Solartraveler/solarclock/minimatrix/software/matrix-advancedclock/menudata-progmem.c

/*You may need to add #include <avr/pgmspace.h> where you included this file */
const unsigned char menudata[] PROGMEM = {
4, 10, 101, 0, 0, 245, 11, 9, 0, 0, 0, 2, 0, 0, 8, 0, 
0, 14, 10, 1, 1, 0, 130, 6, 10, 2, 2, 0, 0, 0, 10, 3, 
3, 0, 0, 0, 10, 100, 4, 0, 47, 1, 9, 0, 0, 0, 2, 0, 
0, 0, 70, 13, 14, 10, 2, 0, 0, 71, 0, 10, 3, 0, 0, 18, 
1, 10, 4, 4, 0, 47, 1, 9, 0, 0, 0, 2, 0, 0, 0, 76, 
13, 14, 10, 2, 0, 0, 100, 0, 10, 3, 0, 0, 42, 0, 10, 4, 
5, 0, 117, 1, 9, 0, 0, 0, 2, 0, 0, 0, 83, 13, 14, 10, 
2, 0, 0, 129, 0, 10, 3, 0, 0, 71, 0, 10, 4, 6, 0, 152, 
1, 9, 0, 0, 0, 2, 0, 0, 0, 90, 13, 14, 10, 2, 0, 0, 
158, 0, 10, 3, 0, 0, 100, 0, 10, 4, 7, 0, 187, 1, 9, 0, 
0, 0, 2, 0, 0, 0, 96, 13, 14, 10, 2, 0, 0, 187, 0, 10, 
3, 0, 0, 129, 0, 10, 4, 8, 0, 222, 1, 9, 0, 0, 0, 2, 
0, 0, 0, 101, 13, 14, 10, 2, 0, 0, 216, 0, 10, 3, 0, 0, 
158, 0, 10, 4, 0, 0, 239, 1, 9, 0, 0, 0, 2, 0, 0, 0, 
108, 13, 14, 10, 2, 0, 0, 245, 0, 10, 3, 0, 0, 187, 0, 10, 
4, 0, 0, 211, 5, 9, 0, 0, 0, 2, 0, 0, 0, 114, 13, 14, 
10, 2, 0, 0, 18, 1, 10, 3, 0, 0, 216, 0, 10, 4, 4, 0, 
34, 12, 9, 0, 0, 0, 2, 0, 0, 0, 122, 13, 15, 10, 2, 0, 
0, 42, 0, 10, 3, 0, 0, 245, 0, 10, 4, 9, 0, 34, 12, 9, 
0, 0, 0, 2, 0, 0, 8, 1, 0, 14, 10, 1, 1, 0, 42, 0, 
10, 2, 10, 0, 82, 1, 10, 3, 5, 0, 117, 1, 10, 4, 7, 0, 
187, 1, 9, 0, 0, 0, 2, 0, 0, 8, 2, 0, 14, 10, 1, 1, 
0, 42, 0, 10, 2, 4, 0, 47, 1, 10, 3, 5, 0, 117, 1, 10, 
4, 7, 0, 187, 1, 9, 0, 0, 0, 2, 0, 0, 8, 3, 0, 14, 
10, 1, 1, 0, 71, 0, 10, 2, 11, 0, 0, 0, 10, 3, 12, 0, 
0, 0, 10, 4, 13, 0, 0, 0, 9, 0, 0, 0, 2, 0, 0, 8, 
4, 0, 14, 10, 1, 1, 0, 100, 0, 10, 2, 14, 0, 0, 0, 10, 
3, 15, 0, 0, 0, 10, 4, 16, 0, 0, 0, 9, 0, 0, 0, 2, 
0, 0, 8, 5, 0, 14, 10, 1, 1, 0, 129, 0, 10, 2, 17, 0, 
0, 0, 10, 3, 18, 0, 0, 0, 10, 4, 19, 0, 0, 0, 9, 0, 
0, 0, 2, 0, 0, 8, 6, 0, 14, 10, 1, 1, 0, 158, 0, 9, 
0, 0, 0, 2, 0, 0, 0, 129, 13, 14, 10, 1, 0, 0, 187, 0, 
10, 2, 0, 0, 18, 2, 10, 3, 0, 0, 217, 3, 10, 4, 20, 0, 
252, 3, 9, 0, 0, 0, 2, 0, 0, 0, 137, 13, 14, 10, 1, 0, 
0, 187, 0, 10, 2, 0, 0, 53, 2, 10, 3, 0, 0, 239, 1, 10, 
4, 0, 0, 31, 4, 9, 0, 0, 0, 2, 0, 0, 0, 144, 13, 14, 
10, 1, 0, 0, 187, 0, 10, 2, 0, 0, 88, 2, 10, 3, 0, 0, 
18, 2, 10, 4, 0, 0, 60, 4, 9, 0, 0, 0, 2, 0, 0, 0, 
151, 13, 14, 10, 1, 0, 0, 187, 0, 10, 2, 0, 0, 123, 2, 10, 
3, 0, 0, 53, 2, 10, 4, 0, 0, 89, 4, 9, 0, 0, 0, 2, 
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
