Solartraveler/solarclock/minimatrix/software/matrix-advancedclock/rc5decoder.h

/************************************************************************/
/*                                                                      */
/*                      RC5 Remote Receiver                             */
/*                                                                      */
/*              Author: Peter Dannegger                                 */
/*                      danni@specs.de                                  */
/*                                                                      */
/************************************************************************/

//connected to PC2
//on of switch on PC1

void rc5Init(void);
void rc5Stop(void);

uint16_t rc5getdata(void);
