Solartraveler/solarclock/minimatrix/software/matrix-advancedclock/gui.c

/* Matrix-Advancedclock
  (c) 2014-2018 by Malte Marwedel
  www.marwedels.de/malte

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
    You should have received a copy of the GNU General Public License
    along with this program; if not, write to the Free Software
    Foundation, Inc., 59 Temple Place, Suite 330, Boston, MA  02111-1307  USA
*/

/* The GUI logic. No AVR specific functions (except loading from flash)
within this file, allows compiling and testing the whole GUI on a PC.
*/

#include <string.h>
#include <stdio.h>
#include <stdint.h>
#include <ctype.h>

#include "config.h"
#include "timeconvert.h"

/*Enable for debug builds.
  Can result in crashes or dark display with no way to get back without
  clearing the EEPRom with a programmer
*/
//#define UNSAFE_OPS

#ifndef PC_BUILD
//AVR only
#include <avr/pgmspace.h>
#include "main.h"
#include "dcf77.h"
#include "displayRtc.h"
#include "rs232.h"
#include "pintest.h"
#include "sound.h"

#else
//PC compatibility layer
#define PROGMEM
#define PSTR(X) X
#define sprintf_P sprintf
#define reboot() printf("reboot()\r\n")
#define dcf77_disable() printf("DCF77 disabled\r\n")
#define dcf77_enable(X) printf("DCF77 enabled\r\n")
#define disp_configure_set(X, Y) printf("disp_configure_set(%i, %i);\r\n", X, Y)
#define rs232_rx_disable() printf("rs232_rx_disable()\r\n")
#define rs232_rx_init() printf("rs232_rx_init()\r\n")
#define pintest_runtest() 0
#define sound_beep(X, Y, Z)

void dcf77_getstatus(char* text);
unsigned char pgm_read_byte(const unsigned char * addr) {
	return *addr;
}

#endif

#include "gui.h"
#include "config.h"

#include "menu-interpreter.h"
#include "menudata-progmem.c"

#define CHARS_PER_MENU_TEXT 14

unsigned char g_StringMenus[MENU_TEXT_MAX*CHARS_PER_MENU_TEXT];

dispUpdateFunc * g_dispUpdate; //NULL is a legitimate value



unsigned char menu_byte_get(MENUADDR addr) {
	if (addr >= MENU_DATASIZE) {
		return 0;
	}
	return pgm_read_byte(menudata+addr);
}

uint8_t updateVoltageText(void) {
	sprintf_P((char*)menu_strings[MENU_TEXT_InputVoltage], PSTR("%umV"), g_state.batVoltage);
	return 1;
}

uint8_t updateCurrentText(void) {
	sprintf_P((char*)menu_strings[MENU_TEXT_ChargerCurrent], PSTR("%imA"), g_state.chargerCurrent);
	return 1;
}

uint8_t updateDcf77Text(void) {
	dcf77_getstatus((char*)menu_strings[MENU_TEXT_DcfValue]);
	return 1;
}

/*
The static variable helps caching the text printing and avoiding calls to
menu_update if nothing changed
*/
uint8_t updateClockTextGeneric(uint8_t clockShowSeconds) {
	static uint8_t slast = 255;
	static uint8_t mlast = 255;
	static uint8_t hlast = 255;
	static uint8_t clockShowSecondslast = 255;
	uint8_t s = g_state.timescache;
	uint8_t m = g_state.timemcache;
	uint8_t h = g_state.timehcache;
	if ((clockShowSeconds != clockShowSecondslast) || (mlast != m) ||
	    (hlast != h) || ((slast != s) && (clockShowSeconds))) {
		clockShowSecondslast = clockShowSeconds;
		slast = s;
		mlast = m;
		hlast = h;
		if (clockShowSeconds) {
			sprintf_P((char*)menu_strings[MENU_TEXT_Clock], PSTR("%2i:%02i:%02i"), h, m, s);
			if (h < 10) {
				menu_strings[MENU_TEXT_Clock][0] = '\t';
			}
		} else {
			sprintf_P((char*)menu_strings[MENU_TEXT_Clock], PSTR("     %2i:%02i"), h, m);
			if (h < 10) {
				menu_strings[MENU_TEXT_Clock][5] = '\t';
			}
		}
		return 1;
	}
	return 0;
}

uint8_t updateClockText(void) {
	return updateClockTextGeneric(g_settings.clockShowSeconds);
}

uint8_t updateClockSetText(void) {
	return updateClockTextGeneric(1);
}

uint8_t updateDateText(void) {
	static uint32_t timelast = 0;
	uint32_t temp = g_state.time;
	if (temp != timelast) {
		timelast = temp;
		uint8_t y;
		uint8_t month;
		uint8_t d;
		dateFromTimestamp(temp, &d, &month, &y, NULL);
		month++; //starts with 0
		d++; //starts with 0
		sprintf_P((char*)menu_strings[MENU_TEXT_Date], PSTR("%02i.%02i.%2i"), (uint16_t)d, (uint16_t)month, (uint16_t)y);
		return 1;
	}
	return 0;
}

uint8_t updateTemperatureText(void) {
	static uint16_t gradcelsiuslast = 0xFFFF;
	if (g_state.gradcelsius10 != gradcelsiuslast) {
		gradcelsiuslast = g_state.gradcelsius10;
		uint16_t gradcelsius10th = g_state.gradcelsius10 % 10;
		uint8_t gradcelsius = g_state.gradcelsius10 / 10;
		sprintf_P((char*)menu_strings[MENU_TEXT_Temperature], PSTR( "%i.%u°C"), gradcelsius, gradcelsius10th);
		return 1;
	}
	return 0;
}

uint8_t updateKeysText(void) {
	sprintf_P((char*)menu_strings[MENU_TEXT_KeyAdValue], PSTR("B:%i"), g_state.keyDebugAd);
	return 1;
}

uint8_t updateConsumptionText(void) {
	uint32_t mah = (g_state.consumption/((uint64_t)60*(uint64_t)60*(uint64_t)1000));
	sprintf_P((char*)menu_strings[MENU_TEXT_ConsumptionTotal], PSTR("%lumAh"), (unsigned long)mah);
	return 1;
}

uint8_t updateAlarmText(void) {
	sprintf_P((char*)menu_strings[MENU_TEXT_Alarm], PSTR("%2i:%02i %s"), g_settings.alarmHour[0], g_settings.alarmMinute[0], g_settings.alarmEnabled[0] ? "On": "--");
	if (g_settings.alarmHour[0] < 10) {
		menu_strings[MENU_TEXT_Alarm][0] = '\t';
	}
	if ((g_state.subsecond & 0x6) == 0) {
		if (g_state.alarmEnterState == 0) {
			menu_strings[MENU_TEXT_Alarm][0] = '\t';
			menu_strings[MENU_TEXT_Alarm][1] = '\t';
		} else if (g_state.alarmEnterState == 1) {
			menu_strings[MENU_TEXT_Alarm][3] = '\t';
			menu_strings[MENU_TEXT_Alarm][4] = '\t';
		} else {
			menu_strings[MENU_TEXT_Alarm][6] = '\t';
			menu_strings[MENU_TEXT_Alarm][7] = '\t';
		}
	}
	return 1;
}

uint8_t updateAlarmadvancedText(void) {
	if (g_state.alarmEnterState <= 2) {
		sprintf_P((char*)menu_strings[MENU_TEXT_Alarmadvanced], PSTR("%2i:%02i %s"), g_settings.alarmHour[1], g_settings.alarmMinute[1], g_settings.alarmEnabled[1] ? "On": "--");
		if (g_settings.alarmHour[1] < 10) {
			menu_strings[MENU_TEXT_Alarmadvanced][0] = '\t';
		}
		if ((g_state.subsecond & 0x6) == 0) {
			if (g_state.alarmEnterState == 0) {
				menu_strings[MENU_TEXT_Alarmadvanced][0] = '\t';
				menu_strings[MENU_TEXT_Alarmadvanced][1] = '\t';
			} else if (g_state.alarmEnterState == 1) {
				menu_strings[MENU_TEXT_Alarmadvanced][3] = '\t';
				menu_strings[MENU_TEXT_Alarmadvanced][4] = '\t';
			} else {
				menu_strings[MENU_TEXT_Alarmadvanced][6] = '\t';
				menu_strings[MENU_TEXT_Alarmadvanced][7] = '\t';
			}
		}
	} else {
		//print enabled weekdays
		uint8_t i;
		uint8_t bitmask = g_settings.alarmWeekdays[1];
		for (i = 0; i < 7; i++) {
			if ((i == g_state.alarmEnterState - 3) && ((g_state.subsecond & 0x6) == 0)) {
				//the value currently edited
				menu_strings[MENU_TEXT_Alarmadvanced][i] = '_';
			} else {
				if (bitmask & 1) {
					menu_strings[MENU_TEXT_Alarmadvanced][i] = '1'+i; //enabled weekday
				} else {
					menu_strings[MENU_TEXT_Alarmadvanced][i] = '-'; //not enabled
				}
			}
			bitmask >>= 1;
		}
	}
	return 1;
}

uint8_t updatePowersavestartText(void) {
	sprintf_P((char*)menu_strings[MENU_TEXT_Powersavestart], PSTR("%2i:%02i"), g_settings.powersaveHourStart, g_settings.powersaveMinuteStart);
	if (g_settings.powersaveHourStart < 10) {
		menu_strings[MENU_TEXT_Powersavestart][0] = '\t';
	}
	if ((g_state.subsecond & 0x6) == 0) {
		if (g_state.powersaveenterstate == 0) {
			menu_strings[MENU_TEXT_Powersavestart][0] = '\t';
			menu_strings[MENU_TEXT_Powersavestart][1] = '\t';
		} else {
			menu_strings[MENU_TEXT_Powersavestart][3] = '\t';
			menu_strings[MENU_TEXT_Powersavestart][4] = '\t';
		}
	}
	return 1;
}

uint8_t updatePowersavestopText(void) {
	sprintf_P((char*)menu_strings[MENU_TEXT_Powersavestop], PSTR("%2i:%02i"), g_settings.powersaveHourStop, g_settings.powersaveMinuteStop);
	if (g_settings.powersaveHourStop < 10) {
		menu_strings[MENU_TEXT_Powersavestop][0] = '\t';
	}
	if ((g_state.subsecond & 0x6) == 0) {
		if (g_state.powersaveenterstate == 0) {
			menu_strings[MENU_TEXT_Powersavestop][0] = '\t';
			menu_strings[MENU_TEXT_Powersavestop][1] = '\t';
		} else {
			menu_strings[MENU_TEXT_Powersavestop][3] = '\t';
			menu_strings[MENU_TEXT_Powersavestop][4] = '\t';
		}
	}
	return 1;
}

uint8_t updatePowersaveweekText(void) {
	uint8_t i;
	uint8_t mask = g_settings.powersaveWeekdays;
	for (i = 0; i < 7; i++) {
		if ((g_state.powersaveenterstate == i) && ((g_state.subsecond & 0x6) == 0)) {
			menu_strings[MENU_TEXT_Powersaveweekdays][i] = '_';
		} else {
			if (mask & 1) {
				menu_strings[MENU_TEXT_Powersaveweekdays][i] = '1'+i;
			} else {
				menu_strings[MENU_TEXT_Powersaveweekdays][i] = '-';
			}
		}
		mask >>= 1;
	}
	return 1;
}

uint8_t updateTimerText(void) {
	if (g_state.timerCountdownSecs) {
		uint8_t h = g_state.timerCountdownSecs / (60*60);
		uint8_t m = g_state.timerCountdownSecs / 60 % 60;
		uint8_t s = g_state.timerCountdownSecs % 60;
		if (h < 10) {
			sprintf_P((char*)menu_strings[MENU_TEXT_Timer], PSTR("   %i:%02i:%02i"), h, m, s);
		} else {
			sprintf_P((char*)menu_strings[MENU_TEXT_Timer], PSTR("%i:%02i:%02i"), h, m, s);
		}
	} else {
		sprintf_P((char*)menu_strings[MENU_TEXT_Timer], PSTR("%imin"), g_settings.timerMinutes);
	}
	return 1;
}

//direct A/D value from LDR
uint8_t updateLightText(void) {
	uint8_t workmode = g_state.ldr >> 14;
	sprintf_P((char*)menu_strings[MENU_TEXT_Light], PSTR("%i:%i"), workmode, g_state.ldr & 0x3FFF);
	return 1;
}

uint8_t updateChargedText(void) {
	uint16_t mah = 0;
	mah = g_state.batteryCharged / (60*60);
	sprintf_P((char*)menu_strings[MENU_TEXT_ChargerCharged], PSTR("%umAh"), mah);
	return 1;
}

//value for driving the display
uint8_t updateDispbrightText(void) {
	if (g_settings.brightnessAuto) {
		sprintf_P((char*)menu_strings[MENU_TEXT_Brightness], PSTR("%i<%i"), g_state.brightnessLdr, g_settings.brightness);
	} else {
		sprintf_P((char*)menu_strings[MENU_TEXT_Brightness], PSTR("%i>%i"), g_state.brightnessLdr, g_settings.brightness);
	}
	return 1;
}

uint8_t updatePerformanceText(void) {
	unsigned int rcperc = g_state.performanceRcRunning * 100 / 256;
	unsigned int cpuperc = g_state.performanceCpuRunning * 100 / 256;
	sprintf_P((char*)menu_strings[MENU_TEXT_Performance], PSTR("%u%%%u%%"), rcperc, cpuperc);
	return 1;
}

uint8_t updateElapsedtimeText(void) {
	uint32_t temp = g_settings.usageseconds;
	uint16_t days = temp / (60UL*60UL*24UL);
	sprintf_P((char*)menu_strings[MENU_TEXT_Elapsedtimemeter], PSTR("%ud"), days);
	return 1;
}

uint8_t updateRc5codeText(void) {
	sprintf_P((char*)menu_strings[MENU_TEXT_Rc5up], PSTR("U:%u"), g_settings.rc5codes[2]);
	sprintf_P((char*)menu_strings[MENU_TEXT_Rc5down], PSTR("D:%u"), g_settings.rc5codes[1]);
	sprintf_P((char*)menu_strings[MENU_TEXT_Rc5left], PSTR("L:%u"), g_settings.rc5codes[0]);
	sprintf_P((char*)menu_strings[MENU_TEXT_Rc5right], PSTR("R:%u"), g_settings.rc5codes[3]);
	return 1;
}

uint8_t updateLoggerText(void) {
	sprintf_P((char*)menu_strings[MENU_TEXT_Logger], PSTR("%ik:%u"), g_state.logger.ksize, g_state.logger.nextentry);
	return 1;
}

uint8_t updateRamText(void) {
	sprintf_P((char*)menu_strings[MENU_TEXT_FreeRam], PSTR("%iByte"), (int)(g_state.memMinStack - g_state.memMaxHeap));
	return 1;
}

/*This function updates all text, which are only changed as response to user
 input. (Not as response to A/D changes or timings*/
static void updateText(void) {
	if (g_settings.debugRs232) {
		sprintf_P((char*)menu_strings[MENU_TEXT_Rs232Debug], PSTR("Dbg On %X"), g_settings.debugRs232);
	} else {
		sprintf_P((char*)menu_strings[MENU_TEXT_Rs232Debug], PSTR("Dbg Off"));
	}
	sprintf_P((char*)menu_strings[MENU_TEXT_Refresh], PSTR("%iHz"), g_settings.displayRefresh);
	sprintf_P((char*)menu_strings[MENU_TEXT_SoundFreq], PSTR("%iHz"), g_settings.soundFrequency);
	sprintf_P((char*)menu_strings[MENU_TEXT_SoundVolume], PSTR("Vol %i"), g_settings.soundVolume);
	sprintf_P((char*)menu_strings[MENU_TEXT_SoundAutoOffTime], PSTR("%imin"), g_settings.soundAutoOffMinutes);
	sprintf_P((char*)menu_strings[MENU_TEXT_BatCap], PSTR("%imAh"), g_settings.batteryCapacity);
	sprintf_P((char*)menu_strings[MENU_TEXT_LedCurrent], PSTR("%iµA"), g_settings.consumptionLedOneMax);
	sprintf_P((char*)menu_strings[MENU_TEXT_CalibRes], PSTR("%i0mΩ"), g_settings.currentResCal);
	sprintf_P((char*)menu_strings[MENU_TEXT_Dcf77Level], PSTR("E<=%i"), g_settings.dcf77Level);
	sprintf_P((char*)menu_strings[MENU_TEXT_Rebootcounter], PSTR("%lu"), (long)g_settings.reboots);
	sprintf_P((char*)menu_strings[MENU_TEXT_Dcf77Period], PSTR("D P: %ih"), g_settings.dcf77Period);
	sprintf_P((char*)menu_strings[MENU_TEXT_LoggerPeriod], PSTR("L P: %ih"), g_settings.loggerPeriod);
	sprintf_P((char*)menu_strings[MENU_TEXT_ClockCalibrate], PSTR("%ims/d"), g_settings.timeCalib);
	sprintf_P((char*)menu_strings[MENU_TEXT_Powersavebattery], PSTR("<%u%%"), g_settings.powersaveBatteryBelow);
	if (g_settings.clockShowSeconds) {
		sprintf_P((char*)menu_strings[MENU_TEXT_ShowSecs], PSTR("Sec On"));
	} else {
		sprintf_P((char*)menu_strings[MENU_TEXT_ShowSecs], PSTR("Sec Off"));
	}
	if (g_settings.brightnessNoOff) {
		sprintf_P((char*)menu_strings[MENU_TEXT_BrigthAlways], PSTR("Min Br 1"));
	} else {
		sprintf_P((char*)menu_strings[MENU_TEXT_BrigthAlways], PSTR("Min Br 0"));
	}
	if (g_settings.chargerMode == 0) {
		sprintf_P((char*)menu_strings[MENU_TEXT_ChargerMode], PSTR("Auto"));
	} else if (g_settings.chargerMode == 1) {
		sprintf_P((char*)menu_strings[MENU_TEXT_ChargerMode], PSTR("Off"));
	} else {
		sprintf_P((char*)menu_strings[MENU_TEXT_ChargerMode], PSTR("On"));
	}
	if (g_settings.rfm12mode == 0) {
		sprintf_P((char*)menu_strings[MENU_TEXT_Rfm12enabled], PSTR("Alw off"));
	} else if (g_settings.rfm12mode == 1) {
		sprintf_P((char*)menu_strings[MENU_TEXT_Rfm12enabled], PSTR("OD 1min"));
	} else if (g_settings.rfm12mode == 2) {
		sprintf_P((char*)menu_strings[MENU_TEXT_Rfm12enabled], PSTR("OD 5min"));
	} else if (g_settings.rfm12mode == 3) {
		sprintf_P((char*)menu_strings[MENU_TEXT_Rfm12enabled], PSTR("Alw on"));
	}
	if (g_settings.rc5mode == 0) {
		sprintf_P((char*)menu_strings[MENU_TEXT_Rc5enabled], PSTR("Alw off"));
	} else if (g_settings.rc5mode == 1) {
		sprintf_P((char*)menu_strings[MENU_TEXT_Rc5enabled], PSTR("OD 1min"));
	} else if (g_settings.rc5mode == 2) {
		sprintf_P((char*)menu_strings[MENU_TEXT_Rc5enabled], PSTR("OD 5min"));
	} else if (g_settings.rc5mode == 3) {
		sprintf_P((char*)menu_strings[MENU_TEXT_Rc5enabled], PSTR("Alw on"));
	}
	if (g_state.pintesterrors) {
		sprintf_P((char*)menu_strings[MENU_TEXT_Pintest], PSTR("Fail"));
	} else {
		sprintf_P((char*)menu_strings[MENU_TEXT_Pintest], PSTR("OK"));
	}
	if (g_settings.summertimeadjust) {
		sprintf_P((char*)menu_strings[MENU_TEXT_Summertime], PSTR("Adj auto"));
	} else {
		sprintf_P((char*)menu_strings[MENU_TEXT_Summertime], PSTR("Adj off"));
	}
	sprintf_P((char*)menu_strings[MENU_TEXT_Rfm12passkey], PSTR("Key %03u"), g_settings.rfm12passcode);
	if (g_settings.flickerWorkaround) {
		sprintf_P((char*)menu_strings[MENU_TEXT_FlickerWorkaround], PSTR("Fix on"));
	} else {
		sprintf_P((char*)menu_strings[MENU_TEXT_FlickerWorkaround], PSTR("Fix off"));
	}
}

static uint8_t dcf77On(void) {
	dcf77_enable(g_state.freqdelta);
	return 1;
}

static uint8_t dcf77Off(void) {
	dcf77_disable();
	return 1;
}

static uint8_t alarmDec(uint8_t alarmid) {
	if ((alarmid == 0) && (g_state.alarmEnterState > 2)) {
		g_state.alarmEnterState = 2; //otherwise we could edit invisible state of alarm 1
	}
	if (g_state.alarmEnterState == 0) {
		g_settings.alarmHour[alarmid]--;
		if (g_settings.alarmHour[alarmid] >= 24) {
			g_settings.alarmHour[alarmid] = 23;
		}
	}
	if (g_state.alarmEnterState == 1) {
		g_settings.alarmMinute[alarmid]--;
		if (g_settings.alarmMinute[alarmid] >= 60) {
			g_settings.alarmMinute[alarmid] = 59;
		}
	}
	if (g_state.alarmEnterState == 2) {
		g_settings.alarmEnabled[alarmid] = 0;
	}
	if (g_state.alarmEnterState > 2) {
		g_settings.alarmWeekdays[alarmid] &= ~(1 << (g_state.alarmEnterState-3)); //clear weekday bit
	}
	return 0;
}

static uint8_t alarmInc(uint8_t alarmid) {
	if ((alarmid == 0) && (g_state.alarmEnterState > 2)) {
		g_state.alarmEnterState = 2; //otherwise we could edit invisible state of alarm 1
	}
	if (g_state.alarmEnterState == 0) {
		g_settings.alarmHour[alarmid]++;
		if (g_settings.alarmHour[alarmid] >= 24) {
			g_settings.alarmHour[alarmid] = 0;
		}
	}
	if (g_state.alarmEnterState == 1) {
		g_settings.alarmMinute[alarmid]++;
		if (g_settings.alarmMinute[alarmid] >= 60) {
			g_settings.alarmMinute[alarmid] = 0;
		}
	}
	if (g_state.alarmEnterState == 2) {
		g_settings.alarmEnabled[alarmid] = 1;
	}
	if (g_state.alarmEnterState > 2) {
		g_settings.alarmWeekdays[alarmid] |= (1 << (g_state.alarmEnterState-3)); //set weekday bit
	}
	return 0;
}

static uint8_t alarmNext(uint8_t alarmid) {
	g_state.alarmEnterState++;
	if (((g_state.alarmEnterState >= 3) && (alarmid == 0)) || (g_state.alarmEnterState >= 10)) {
		g_state.alarmEnterState = 0;
	}
	return 0;
}

static uint8_t timerDec(void) {
	if (g_state.timerCountdownSecs == 0) {
		if (g_settings.timerMinutes >= 25) {
			g_settings.timerMinutes -= 4;
		}
		if (g_settings.timerMinutes >= 2) {
			g_settings.timerMinutes--;
		}
	}
	return 0;
}

static uint8_t timerInc(void) {
	if (g_state.timerCountdownSecs == 0) {
		if (g_settings.timerMinutes < 180) {
			if (g_settings.timerMinutes >= 20) {
				g_settings.timerMinutes += 4;
			}
			g_settings.timerMinutes++;
		}
	}
	return 0;
}

static uint8_t timerStart(void) {
	if (g_state.timerCountdownSecs) {
		g_state.timerCountdownSecs = 0; //abort running timer
	} else {
		g_state.timerCountdownSecs = g_settings.timerMinutes*60; //start timer
	}
	return 0;
}

static uint8_t brightDec(void) {
#ifdef UNSAFE_OPS
	if (g_settings.brightness > 0) //can result in a permanently dark screen and blind navigation
#else
	if (g_settings.brightness > 1)
#endif
	{
#if 1
		if (g_settings.brightness >= 80) {
			g_settings.brightness -= 20;
		} else if (g_settings.brightness >= 15) {
			g_settings.brightness -= 5;
		} else {
			g_settings.brightness--;
		}
#else
		g_settings.brightness--;
#endif
	}
	return 0;
}

static uint8_t brightInc(void) {
#if 1
	if ((g_settings.brightness >= 60) && (g_settings.brightness < 235)) {
		g_settings.brightness += 20;
	} else if ((g_settings.brightness >= 10) && (g_settings.brightness < 250)) {
		g_settings.brightness += 5;
	} else {
		if (g_settings.brightness < 255) {
			g_settings.brightness++;
		}
	}
#else
	g_settings.brightness++;
#endif
	return 0;
}

static uint8_t brightAutoToggle(void) {
	g_settings.brightnessAuto = 1 - g_settings.brightnessAuto;
	return 0;
}

static uint8_t brightAlwaysOn(void) {
	g_settings.brightnessNoOff = 1;
	updateText();
	return 1;
}

static uint8_t brightAlwaysOff(void) {
	g_settings.brightnessNoOff = 0;
	updateText();
	return 1;
}

static uint8_t clockShowSecOff(void) {
	g_settings.clockShowSeconds = 0;
	updateText();
	return 1;
}

static uint8_t clockShowSecOn(void) {
	g_settings.clockShowSeconds = 1;
	updateText();
	return 1;
}

static uint8_t soundAutoOffDec(void) {
	if (g_settings.soundAutoOffMinutes >= 2) {
		g_settings.soundAutoOffMinutes--;
	}
	updateText();
	return 1;
}

static uint8_t soundAutoOffInc(void) {
	if (g_settings.soundAutoOffMinutes < 30) {
		g_settings.soundAutoOffMinutes++;
	}
	updateText();
	return 1;
}

static uint8_t soundVolumeDec(void) {
	if (g_settings.soundVolume >= 5) {
		g_settings.soundVolume -= 5;
	}
	updateText();
	sound_beep(g_settings.soundVolume, g_settings.soundFrequency, 100);
	return 1;
}

static uint8_t soundVolumeInc(void) {
	if (g_settings.soundVolume <= 250) {
		g_settings.soundVolume += 5;
	}
	updateText();
	sound_beep(g_settings.soundVolume, g_settings.soundFrequency, 100);
	return 1;
}

static uint8_t soundFreqDec(void) {
	if (g_settings.soundFrequency >= 200) {
		g_settings.soundFrequency -= 100;
	}
	updateText();
	sound_beep(g_settings.soundVolume, g_settings.soundFrequency, 100);
	return 1;
}

static uint8_t soundFreqInc(void) {
	if (g_settings.soundFrequency <= 1900) {
		g_settings.soundFrequency += 100;
	}
	updateText();
	sound_beep(g_settings.soundVolume, g_settings.soundFrequency, 100);
	return 1;
}

static uint8_t refreshDec(void) {
	if (g_settings.displayRefresh >= 75) {
		g_settings.displayRefresh -= 25;
	}
	updateText();
	disp_configure_set(g_state.brightness, g_settings.displayRefresh);
	return 1;
}

static uint8_t refreshInc(void) {
#ifdef UNSAFE_OPS
	if (g_settings.displayRefresh <= 3000)
#else
	if (g_settings.displayRefresh <= 225)
#endif
	{
		g_settings.displayRefresh += 25;
	}
	updateText();
	disp_configure_set(g_state.brightness, g_settings.displayRefresh);
	return 1;
}

static uint8_t chargerDec(void) {
	if (g_settings.chargerMode) {
		g_settings.chargerMode--;
	}
	updateText();
	return 1;
}

static uint8_t chargerInc(void) {
	if (g_settings.chargerMode <= 1) {
		g_settings.chargerMode++;
	}
	updateText();
	return 1;
}

static uint8_t rs232Dec(void) {
	if (g_settings.debugRs232) {
		g_settings.debugRs232--;
	}
	if (g_settings.debugRs232 < 2) {
		rs232_rx_disable();
	}
	updateText();
	return 1;
}

static uint8_t rs232Inc(void) {
	if (g_settings.debugRs232 < 15) {
		g_settings.debugRs232++;
	}
	if (g_settings.debugRs232 == 2) {
		rs232_rx_init();
	}
	updateText();
	return 1;
}

static uint8_t batCapDec(void) {
	if (g_settings.batteryCapacity > BATTERYCAPACITY_MIN) {
		g_settings.batteryCapacity -= 50;
	}
	updateText();
	return 1;
}

static uint8_t batCapInc(void) {
	if (g_settings.batteryCapacity < BATTERYCAPACITY_MAX) {
		g_settings.batteryCapacity += 50;
	}
	updateText();
	return 1;
}

static uint8_t ledCurrDec(void) {
	if (g_settings.consumptionLedOneMax > CONSUMPTIONLEDONEMAX_MIN) {
		g_settings.consumptionLedOneMax -= 10;
	}
	updateText();
	return 1;
}

static uint8_t ledCurrInc(void) {
	if (g_settings.consumptionLedOneMax < CONSUMPTIONLEDONEMAX_MAX) {
		g_settings.consumptionLedOneMax += 10;
	}
	updateText();
	return 1;
}

static uint8_t calRes46Dec(void) {
	if (g_settings.currentResCal > CURRENTRESCAL_MIN) {
		g_settings.currentResCal--;
	}
	updateText();
	return 1;
}

static uint8_t calRes46Inc(void) {
	if (g_settings.currentResCal < CURRENTRESCAL_MAX) {
		g_settings.currentResCal++;
	}
	updateText();
	return 1;
}

static uint8_t dcf77LevelDec(void) {
	if (g_settings.dcf77Level > DCF77LEVEL_MIN) {
		g_settings.dcf77Level--;
	}
	updateText();
	return 1;
}

static uint8_t dcf77LevelInc(void) {
	if (g_settings.dcf77Level < DCF77LEVEL_MAX) {
		g_settings.dcf77Level++;
	}
	updateText();
	return 1;
}

static uint8_t powersavestartDec(void) {
	if (g_state.powersaveenterstate == 0) {
		g_settings.powersaveHourStart--;
		if (g_settings.powersaveHourStart > 23) {
			g_settings.powersaveHourStart = 23;
		}
	} else {
		g_settings.powersaveMinuteStart--;
		if (g_settings.powersaveMinuteStart > 59) {
			g_settings.powersaveMinuteStart = 59;
		}
	}
	updateText();
	return 1;
}

static uint8_t powersavestartInc(void) {
	if (g_state.powersaveenterstate == 0) {
		g_settings.powersaveHourStart++;
		if (g_settings.powersaveHourStart > 23) {
			g_settings.powersaveHourStart = 0;
		}
	} else {
		g_settings.powersaveMinuteStart++;
		if (g_settings.powersaveMinuteStart > 59) {
			g_settings.powersaveMinuteStart = 0;
		}
	}
	updateText();
	return 1;
}

static uint8_t powersavestartNext(void) {
	g_state.powersaveenterstate = (g_state.powersaveenterstate + 1) & 1;
	updateText();
	return 1;
}

static uint8_t powersavestopDec(void) {
	if (g_state.powersaveenterstate == 0) {
		g_settings.powersaveHourStop--;
		if (g_settings.powersaveHourStop > 23) {
			g_settings.powersaveHourStop = 23;
		}
	} else {
		g_settings.powersaveMinuteStop--;
		if (g_settings.powersaveMinuteStop > 59) {
			g_settings.powersaveMinuteStop = 59;
		}
	}
	updateText();
	return 1;
}

static uint8_t powersavestopInc(void) {
	if (g_state.powersaveenterstate == 0) {
		g_settings.powersaveHourStop++;
		if (g_settings.powersaveHourStop > 23) {
			g_settings.powersaveHourStop = 0;
		}
	} else {
		g_settings.powersaveMinuteStop++;
		if (g_settings.powersaveMinuteStop > 59) {
			g_settings.powersaveMinuteStop = 0;
		}
	}
	updateText();
	return 1;
}

static uint8_t powersavestopNext(void) {
	g_state.powersaveenterstate = (g_state.powersaveenterstate + 1) & 1;
	updateText();
	return 1;
}

static uint8_t powersaveweekDec(void) {
	g_settings.powersaveWeekdays &= ~(1<<g_state.powersaveenterstate);
	updateText();
	return 1;
}

static uint8_t powersaveweekInc(void) {
	g_settings.powersaveWeekdays |= (1<<g_state.powersaveenterstate);
	updateText();
	return 1;
}

static uint8_t powersaveweekNext(void) {
	g_state.powersaveenterstate++;
	if (g_state.powersaveenterstate >= 7) {
		g_state.powersaveenterstate = 0;
	}
	updateText();
	return 1;
}

static uint8_t powersaveOn(void) {
	g_state.powersaveEnabled |= 2; //manual mode. cant be disabled by timer
	g_dispUpdate = &updateClockText;
	return 1;
}

static uint8_t powersavebatInc(void) {
	if (g_settings.powersaveBatteryBelow < 100) {
		g_settings.powersaveBatteryBelow += 5;
	}
	updateText();
	return 1;
}

static uint8_t powersavebatDec(void) {
	if (g_settings.powersaveBatteryBelow >= 5) {
		g_settings.powersaveBatteryBelow -= 5;
	}
	updateText();
	return 1;
}


static uint8_t keylockLeave(void) {
	g_state.powersaveEnabled &= ~2; //clear manual mode bit
	g_state.keylockTimeoutCd = 0; //stop some timeout
	g_dispUpdate = &updateClockText;
	return 1;
}


static uint8_t rfm12Dec(void) {
	if (g_settings.rfm12mode > 0) {
		g_settings.rfm12mode--;
	}
	updateText();
	return 1;
}

static uint8_t rfm12Inc(void) {
	if (g_settings.rfm12mode < 3) {
		g_settings.rfm12mode++;
	}
	updateText();
	return 1;
}

static uint8_t rc5Dec(void) {
	if (g_settings.rc5mode > 0) {
		g_settings.rc5mode--;
	}
	updateText();
	return 1;
}

static uint8_t rc5Inc(void) {
	if (g_settings.rc5mode < 3) {
		g_settings.rc5mode++;
	}
	updateText();
	return 1;
}

static uint8_t rc5recordDisable(void) {
	g_dispUpdate = NULL;
	g_state.rc5entermode = 0;
	return 0;
}

static uint8_t rc5recordDown(void) {
	g_dispUpdate = updateRc5codeText;
	g_state.rc5entermode = 2;
	return 0;
}

static uint8_t rc5recordLeft(void) {
	g_dispUpdate = updateRc5codeText;
	g_state.rc5entermode = 1;
	return 0;
}

static uint8_t rc5recordUp(void) {
	g_dispUpdate = updateRc5codeText;
	g_state.rc5entermode = 3;
	return 0;
}

static uint8_t rc5recordRight(void) {
	g_dispUpdate = updateRc5codeText;
	g_state.rc5entermode = 4;
	return 0;
}

static uint8_t pintestStart(void) {
	g_state.pintesterrors = pintest_runtest();
	updateText();
	return 1;
}

static uint8_t summertimeAuto(void) {
	g_settings.summertimeadjust = 1;
	updateText();
	return 1;
}

static uint8_t summertimeOff(void) {
	g_settings.summertimeadjust = 0;
	updateText();
	return 1;
}

static uint8_t rfm12PasskeyMod(uint8_t index) {
	uint8_t val[3];
	if (index < 3) {
		val[0] = g_settings.rfm12passcode % 10;
		val[1] = (g_settings.rfm12passcode / 10) % 10;
		val[2] = (g_settings.rfm12passcode / 100);
		val[index] = (val[index] + 1 ) % 10;
		g_settings.rfm12passcode = val[2]*100 + val[1]*10 + val[0];
	}
	updateText();
	return 1;
}

#define PERIODTIMES 6
const uint8_t periodTimes[PERIODTIMES] = {1, 2, 4, 6, 12, 24};

static uint8_t gui_PeriodIndex(uint8_t value) {
	uint8_t i = 0;
	for (i = 0; i < PERIODTIMES; i++) {
		if (periodTimes[i] == value) {
			return i;
		}
	}
	return 0;
}

static uint8_t gui_PeriodNext(uint8_t value) {
	uint8_t index = gui_PeriodIndex(value);
	if ((index+1) < PERIODTIMES) {
		return periodTimes[index+1];
	}
	return periodTimes[index];
}

static uint8_t gui_PeriodPrev(uint8_t value) {
	uint8_t index = gui_PeriodIndex(value);
	if ((index > 0) && (index <= PERIODTIMES)) {
		return periodTimes[index-1];
	}
	return periodTimes[0];
}

static uint8_t dcf77PeriodInc(void) {
	g_settings.dcf77Period = gui_PeriodNext(g_settings.dcf77Period);
	updateText();
	return 1;
}

static uint8_t dcf77PeriodDec(void) {
	g_settings.dcf77Period = gui_PeriodPrev(g_settings.dcf77Period);
	updateText();
	return 1;
}

static uint8_t loggerPeriodInc(void) {
	g_settings.loggerPeriod = gui_PeriodNext(g_settings.loggerPeriod);
	updateText();
	return 1;
}

static uint8_t loggerPeriodDec(void) {
	g_settings.loggerPeriod = gui_PeriodPrev(g_settings.loggerPeriod);
	updateText();
	return 1;
}

static uint8_t flickerWorkaroundOff(void) {
	g_settings.flickerWorkaround = 0;
	updateText();
	return 1;
}

static uint8_t flickerWorkaroundOn(void) {
	g_settings.flickerWorkaround = 1;
	updateText();
	return 1;
}

static uint8_t chargerChargedDec(void) {
	if (g_state.batteryCharged > 60UL*60UL) {
		g_state.batteryCharged -= 60UL*60UL; //sub 1mAh
	}
	updateText();
	return 1;
}

static uint8_t chargerChargedInc(void) {
	uint32_t batmax = g_settings.batteryCapacity*60UL*60UL;
	if (g_state.batteryCharged < batmax) {
		g_state.batteryCharged += 60UL*60UL; //add 1mAh
	}
	updateText();
	return 1;
}

static uint8_t timeManualHourInc(void) {
	g_state.timehcache++;
	if (g_state.timehcache >= 24) g_state.timehcache = 0;
	g_state.time = ((((g_state.time / (60UL*60UL*24UL)) * 24UL) + (uint32_t)g_state.timehcache)* 60UL + (uint32_t)g_state.timemcache) * 60UL + g_state.timescache;
	updateClockSetText();
	return 1;
}

static uint8_t timeManualMinInc(void) {
	g_state.timemcache++;
	if (g_state.timemcache >= 60) g_state.timemcache = 0;
	g_state.time = (((g_state.time / (60UL*60UL)) * 60UL) + g_state.timemcache)* 60L + g_state.timescache;
	updateClockSetText();
	return 1;
}

static uint8_t timeManualSecZero(void) {
	g_state.timescache = 0;
	g_state.time = g_state.time / 60 * 60; //clear out the seconds
	updateClockSetText();
	return 1;
}

static uint8_t dateManualDayInc(void) {
	//split seconds up
	uint8_t month;
	uint8_t d;
	uint8_t y;
	uint32_t clock = dateFromTimestamp(g_state.time, &d, &month, &y, NULL);
	uint8_t daysinmonth = daysInMonth(month, y);
	//increment
	d++;
	if (d >= daysinmonth) {
		d = 0;
	}
	//merge togehter
	g_state.time = timestampFromDate(d, month, y, clock);
	updateDateText();
	return 1;
}

static uint8_t dateManualMonthInc(void) {
	//split seconds up
	uint8_t month;
	uint8_t d;
	uint8_t y;
	uint32_t clock = dateFromTimestamp(g_state.time, &d, &month, &y, NULL);
	//increment
	month++;
	if (month >= 12) {
		month = 0;
	}
	uint8_t daysinnewmonth = daysInMonth(month, y);
	if (d >= daysinnewmonth) {
		d = daysinnewmonth-1;
	}
	//merge togehter
	g_state.time = timestampFromDate(d, month, y, clock);
	updateDateText();
	return 1;
}

static uint8_t dateManualYearInc(void) {
	//split seconds up
	uint8_t month;
	uint8_t d;
	uint8_t y;
	uint32_t clock = dateFromTimestamp(g_state.time, &d, &month, &y, NULL);
	//increment
	y++;
	if (y >= 100) {
		y = 0;
	}
	uint8_t daysinnewmonth = daysInMonth(month, y);
	if (d >= daysinnewmonth) {
		d = daysinnewmonth-1;
	}
	//merge togehter
	g_state.time = timestampFromDate(d, month, y, clock);
	updateDateText();
	return 1;
}

static uint8_t clockCalibInc(void) {
	if (g_settings.timeCalib < TIMECALIB_MAX) {
		g_settings.timeCalib += -(g_settings.timeCalib % 50) + 50;
	}
	updateText();
	return 1;
}

static uint8_t clockCalibDec(void) {
	if (g_settings.timeCalib > TIMECALIB_MIN) {
		g_settings.timeCalib -= (g_settings.timeCalib % 50) + 50;
	}
	updateText();
	return 1;
}

static uint8_t clockCalibAuto(void) {
	g_settings.timeCalib = g_state.timeLastDelta;
	updateText();
	return 1;
}

static uint8_t KeylockCountdownRestart(void) {
	g_state.keylockTimeoutCd = 60;
	return 0;
}

unsigned char menu_action(unsigned short action) {
	unsigned char redraw = 0;
	switch(action) {
		case MENU_ACTION_ShowVoltageOn:      g_dispUpdate = &updateVoltageText; break;
		case MENU_ACTION_ShowCurrentOn:      g_dispUpdate = &updateCurrentText; break;
		case MENU_ACTION_ShowLightOn:        g_dispUpdate = &updateLightText; break;
		case MENU_ACTION_ShowDCF77On:        g_dispUpdate = &updateDcf77Text; break;
		case MENU_ACTION_ShowClockOn:        g_dispUpdate = &updateClockText; break;
		case MENU_ACTION_ShowClockSetOn:     g_dispUpdate = &updateClockSetText; break;
		case MENU_ACTION_ShowDateOn:         g_dispUpdate = &updateDateText; break;
		case MENU_ACTION_ShowTemperatureOn:  g_dispUpdate = &updateTemperatureText; break;
		case MENU_ACTION_ShowKeysOn:         g_dispUpdate = &updateKeysText; break;
		case MENU_ACTION_ShowConsumptionOn:  g_dispUpdate = &updateConsumptionText; break;
		case MENU_ACTION_ShowDispbrightOn:   g_dispUpdate = &updateDispbrightText; break;
		case MENU_ACTION_ShowTimerOn:        g_dispUpdate = &updateTimerText; break;
		case MENU_ACTION_ShowAlarmOn:        g_dispUpdate = &updateAlarmText; break;
		case MENU_ACTION_ShowAlarmadvancedOn: g_dispUpdate = &updateAlarmadvancedText; break;
		case MENU_ACTION_ShowChargedOn:      g_dispUpdate = &updateChargedText; break;
		case MENU_ACTION_ShowPerformanceOn:  g_dispUpdate = &updatePerformanceText; break;
		case MENU_ACTION_ShowElapsedtimeOn:  g_dispUpdate = &updateElapsedtimeText; break;
		case MENU_ACTION_ShowPowersavestartOn:g_dispUpdate = &updatePowersavestartText; break;
		case MENU_ACTION_ShowPowersavestopOn:g_dispUpdate = &updatePowersavestopText; break;
		case MENU_ACTION_ShowPowersaveweekOn:g_dispUpdate = &updatePowersaveweekText; break;
		case MENU_ACTION_ShowLoggerOn:       g_dispUpdate = &updateLoggerText; break;
		case MENU_ACTION_ShowRamOn:          g_dispUpdate = &updateRamText; break;
		case MENU_ACTION_DisplayUpdateOff:   g_dispUpdate = NULL; break;
		case MENU_ACTION_Dcf77Off:           redraw = dcf77Off(); break;
		case MENU_ACTION_Dcf77On:            redraw = dcf77On(); break;
		case MENU_ACTION_AlarmDec:           redraw = alarmDec(0); break;
		case MENU_ACTION_AlarmInc:           redraw = alarmInc(0); break;
		case MENU_ACTION_AlarmNext:          redraw = alarmNext(0); break;
		case MENU_ACTION_AlarmAdvancedDec:   redraw = alarmDec(1); break;
		case MENU_ACTION_AlarmAdvancedInc:   redraw = alarmInc(1); break;
		case MENU_ACTION_AlarmAdvancedNext:  redraw = alarmNext(1); break;
		case MENU_ACTION_TimerDec:           redraw = timerDec(); break;
		case MENU_ACTION_TimerInc:           redraw = timerInc(); break;
		case MENU_ACTION_TimerStart:         redraw = timerStart(); break;
		case MENU_ACTION_BrightDec:          redraw = brightDec(); break;
		case MENU_ACTION_BrightInc:          redraw = brightInc(); break;
		case MENU_ACTION_BrightAutoToggle:   redraw = brightAutoToggle(); break;
		case MENU_ACTION_BrightAlwaysOff:    redraw = brightAlwaysOff(); break;
		case MENU_ACTION_BrightAlwaysOn:     redraw = brightAlwaysOn(); break;
		case MENU_ACTION_ClockShowSecOff:    redraw = clockShowSecOff(); break;
		case MENU_ACTION_ClockShowSecOn:     redraw = clockShowSecOn(); break;
		case MENU_ACTION_SoundAutoOffDec:    redraw = soundAutoOffDec(); break;
		case MENU_ACTION_SoundAutoOffInc:    redraw = soundAutoOffInc(); break;
		case MENU_ACTION_SoundVolumeDec:     redraw = soundVolumeDec(); break;
		case MENU_ACTION_SoundVolumeInc:     redraw = soundVolumeInc(); break;
		case MENU_ACTION_SoundFreqDec:       redraw = soundFreqDec(); break;
		case MENU_ACTION_SoundFreqInc:       redraw = soundFreqInc(); break;
		case MENU_ACTION_RefreshDec:         redraw = refreshDec(); break;
		case MENU_ACTION_RefreshInc:         redraw = refreshInc(); break;
		case MENU_ACTION_Reboot:             reboot(); break;
		case MENU_ACTION_ChargerDec:         redraw = chargerDec(); break;
		case MENU_ACTION_ChargerInc:         redraw = chargerInc(); break;
		case MENU_ACTION_Rs232Dec:           redraw = rs232Dec(); break;
		case MENU_ACTION_Rs232Inc:           redraw = rs232Inc(); break;
		case MENU_ACTION_BatCapDec:          redraw = batCapDec(); break;
		case MENU_ACTION_BatCapInc:          redraw = batCapInc(); break;
		case MENU_ACTION_LedCurrDec:         redraw = ledCurrDec(); break;
		case MENU_ACTION_LedCurrInc:         redraw = ledCurrInc(); break;
		case MENU_ACTION_CalRes46Dec:        redraw = calRes46Dec(); break;
		case MENU_ACTION_CalRes46Inc:        redraw = calRes46Inc(); break;
		case MENU_ACTION_Dcf77LevelDec:      redraw = dcf77LevelDec(); break;
		case MENU_ACTION_Dcf77LevelInc:      redraw = dcf77LevelInc(); break;
		case MENU_ACTION_PowersavestartDec:  redraw = powersavestartDec(); break;
		case MENU_ACTION_PowersavestartInc:  redraw = powersavestartInc(); break;
		case MENU_ACTION_PowersavestartNext: redraw = powersavestartNext(); break;
		case MENU_ACTION_PowersavestopDec:   redraw = powersavestopDec(); break;
		case MENU_ACTION_PowersavestopInc:   redraw = powersavestopInc(); break;
		case MENU_ACTION_PowersavestopNext:  redraw = powersavestopNext(); break;
		case MENU_ACTION_PowersaveweekDec:   redraw = powersaveweekDec(); break;
		case MENU_ACTION_PowersaveweekInc:   redraw = powersaveweekInc(); break;
		case MENU_ACTION_PowersaveweekNext:  redraw = powersaveweekNext(); break;
		case MENU_ACTION_PowersavebatInc:    redraw = powersavebatInc(); break;
		case MENU_ACTION_PowersavebatDec:    redraw = powersavebatDec(); break;
		case MENU_ACTION_Rfm12Dec:           redraw = rfm12Dec(); break;
		case MENU_ACTION_Rfm12Inc:           redraw = rfm12Inc(); break;
		case MENU_ACTION_Rc5Dec:             redraw = rc5Dec(); break;
		case MENU_ACTION_Rc5Inc:             redraw = rc5Inc(); break;
		case MENU_ACTION_Rc5RecordDisable:   redraw = rc5recordDisable(); break;
		case MENU_ACTION_Rc5RecordDown:      redraw = rc5recordDown(); break;
		case MENU_ACTION_Rc5RecordUp:        redraw = rc5recordUp(); break;
		case MENU_ACTION_Rc5RecordLeft:      redraw = rc5recordLeft(); break;
		case MENU_ACTION_Rc5RecordRight:     redraw = rc5recordRight(); break;
		case MENU_ACTION_PintestStart:       redraw = pintestStart(); break;
		case MENU_ACTION_PowersaveOn:        redraw = powersaveOn(); break;
		case MENU_ACTION_KeylockLeave:       redraw = keylockLeave(); break;
		case MENU_ACTION_SummertimeAuto:     redraw = summertimeAuto(); break;
		case MENU_ACTION_SummertimeOff:      redraw = summertimeOff(); break;
		case MENU_ACTION_Rfm12passkey1:      redraw = rfm12PasskeyMod(0); break;
		case MENU_ACTION_Rfm12passkey10:     redraw = rfm12PasskeyMod(1); break;
		case MENU_ACTION_Rfm12passkey100:    redraw = rfm12PasskeyMod(2); break;
		case MENU_ACTION_Dcf77PeriodInc:     redraw = dcf77PeriodInc(); break;
		case MENU_ACTION_Dcf77PeriodDec:     redraw = dcf77PeriodDec(); break;
		case MENU_ACTION_LoggerPeriodInc:    redraw = loggerPeriodInc(); break;
		case MENU_ACTION_LoggerPeriodDec:    redraw = loggerPeriodDec(); break;
		case MENU_ACTION_FlickerWorkaroundOff: redraw = flickerWorkaroundOff(); break;
		case MENU_ACTION_FlickerWorkaroundOn: redraw = flickerWorkaroundOn(); break;
		case MENU_ACTION_ChargerChargedInc:  redraw = chargerChargedInc(); break;
		case MENU_ACTION_ChargerChargedDec:  redraw = chargerChargedDec(); break;
		case MENU_ACTION_TimeManualHourInc:  redraw = timeManualHourInc(); break;
		case MENU_ACTION_TimeManualMinInc:   redraw = timeManualMinInc(); break;
		case MENU_ACTION_TimeManualSecZero:  redraw = timeManualSecZero(); break;
		case MENU_ACTION_DateManualDayInc:   redraw = dateManualDayInc(); break;
		case MENU_ACTION_DateManualMonthInc: redraw = dateManualMonthInc(); break;
		case MENU_ACTION_DateManualYearInc:  redraw = dateManualYearInc(); break;
		case MENU_ACTION_ClockCalibDec:      redraw = clockCalibDec(); break;
		case MENU_ACTION_ClockCalibInc:      redraw = clockCalibInc(); break;
		case MENU_ACTION_ClockCalibAuto:     redraw = clockCalibAuto(); break;
		case MENU_ACTION_KeylockCountdownRestart: g_dispUpdate = NULL; redraw = KeylockCountdownRestart(); break;
	}
	if (g_dispUpdate) {
		g_dispUpdate();
		redraw = 1;
	}
	return redraw;
}

//the global settings should be loaded before calling this function
void gui_init(void) {
	uint8_t i;
	for (i = 0; i < MENU_TEXT_MAX; i++) {
		menu_strings[i] = g_StringMenus + i*CHARS_PER_MENU_TEXT;
	}
	updateText();
	g_dispUpdate = &updateDcf77Text; //This is for the first screen shown on startup
	g_dispUpdate();
	menu_redraw();
}
