Solartraveler/solarclock/minimatrix/software/matrix-simpleclock/displayRtc.c

/* Matrix-Simpleclock
  (c) 2014-2017 by Malte Marwedel
  www.marwedels.de/malte

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
    You should have received a copy of the GNU General Public License
    along with this program; if not, write to the Free Software
    Foundation, Inc., 59 Temple Place, Suite 330, Boston, MA  02111-1307  USA
*/

#include <avr/interrupt.h>
#include <avr/io.h>
#include <util/delay_basic.h>
#include <string.h>
#include <stdio.h>
#include <avr/cpufunc.h>

#include "displayRtc.h"
#include "main.h"
#include "rs232.h"
#include "debug.h"
#include "config.h"

#include "menu-interpreter-config.h"
#include "menu-interpreter.h"


#define DISP_ROWS MENU_SCREEN_Y
#define DISP_COLUMS MENU_SCREEN_X
#define DISP_COLUM_BYTES ((DISP_COLUMS+7)/8)
#define DISP_TOTAL_BYTES (DISP_COLUM_BYTES*DISP_ROWS)

/*
Tests have shown that the flicker (loose of interrupt) is gone if the compare
  value is always increased by at least 7.
  A value of 6 has several misses per second.
  constant evaluates to 428 with cycles = 7:
Update:
  As a value of 7 still does result in occassional flicker when RC power saving
  is enabled (FBugfix = Fix off), we increase the value to 8, however all values
  in the explanations are still valid for a value of 7.
*/
#define RTC_REQUIRED_SYNC_CYCLES 8

#define DISP_WITHIN_INT_LIMIT (F_CPU*RTC_REQUIRED_SYNC_CYCLES/F_RTC)

/*We use the measured values from the tests (see below) and make sure the value
  is 23 for 2MHz CPU frequency.
 */
#define DISP_RFM12_PERMIT_MAX (F_CPU /86956)

//we use double-buffering, and this is the hidden buffer
uint8_t disp_backbuffer[DISP_TOTAL_BYTES];
//the acutal buffer to be drawn
volatile uint8_t disp_buffer[DISP_TOTAL_BYTES];

//current active line on the driver. 0...4 active line. 5: dark line
volatile uint8_t disp_row;

//used for low brightness values (= 4*CPU cycles)
volatile uint8_t disp_timing_active_delay_cycles;

//used for high and maximum brightness values
volatile uint16_t disp_timing_active_rtc;

//used for high brightness values
volatile uint16_t disp_timing_idle_rtc;

//used for low brightness values
volatile uint16_t disp_timing_idle_line_rtc;

//copy of RTC.COMP
volatile uint16_t disp_rtc_comp;

volatile uint8_t rtc_8thcounter;

uint16_t disp_rtc_per = DISP_RTC_PER; //this is adjusted slightly by +-2 for increasing precision

//the first value is a dummy value
uint8_t const disp_linebits[MENU_SCREEN_Y+2] = {0, (1<<4), (1<<5), (1<<6), (1<<7), (1<<6), 0};


/* There are four different modes of operation, depending on the selected
   brighness.
   Maximum brightness: Set next line, update next interrupt value to the row ON
                   time. Never dark -> 5 interrupts per refresh
                    >>5x interrupt after disp_timing_active_rtc cycles<<
   High brighness: Set next line, update next interrupt value to the row ON
                   time. After 5 rows, leave OFF and update interrupt value
                   for the time of darkness of all rows.
                   -> 6 interrupts per refresh
                   >>5x interrupt after disp_timing_active_rtc cycles<<
                   >>1x interrupt after disp_timing_idle_rtc cycles<<
   Low brightness: Set next line, wait within the interrupt, and set to off,
                   then set the next interrupt to the time of a single line
                   being dark. -> 5 interrupts per refresh
                   >>5x interrupt after disp_timing_idle_line_rtc<<
                   >>AND each interrupt take an additional
                   >>4*disp_timing_active_delay_cycles CPU cycles<<
                   -> Known bug: When DCF77 analysis increases its clock,
                   the LEDs will become darker if LEDs are in this mode -> wont
                   fix.
   LEDs off:       The compare interrupt is disabled, no wakeup

The whole interrupt handler can take up to
~594 clock cycles (including 428 wait cycles) excluding sync cycles
-> 166...200 cycles expected minimum.
sync might take three clock crystal cycles -> + 183 cycles -> 777 cycles (combined)
->0.39ms

Trying to reduce this, as the sync cycles did not fix the random flicker problem:
~594 cycles -> 0.297ms

We need a value of less than ~0.3ms otherwise RFM12 communication wont
keep its timing @ 10kBaud.

So in order to make sure such critical timings wont happe, we make a gap
in brightness regulation where the waiting time in the interrupt is 6 RTC cycles.
This results in 532 (=594-428+366) -> 0.266ms waiting time -> fits.

However, experiments show:
Good case with RFM12 working:
tOnR:7 tOffR:290 tOnC:23 tOffLr:64
Bad case, RFM12 still working, but a lot of errors:
tOnR:7 tOffR:290 tOnC:27 tOffLr:64
only paritally data:
tOnR:7 tOffR:290 tOnC:43 tOffLr:63
no data:
tOnR:7 tOffR:290 tOnC:58 tOffLr:62

So we need to increase the brigness once more if the RFM12 is active.
(An alternate solution would be to decrease the RFM12 baudrate to work with
less frequent polling)
So tOnC must stay <= 23

The limit @100Hz between low and hight brightness are number 26 (low) and 27 (high).
As result the requested brighness for values 8...28 are resulting in a
brighness of 28 as long as the RFM12 is enabled.
*/
static void disp_update_line(void) {
	uint8_t disp_row_l = disp_row;
	uint16_t update_rtc_ticks = 0;
	//1. all rows (lines) off
	PORTE.OUTSET = (1<<6);
	PORTK.OUT = 0xFF;
	//update line bits out line
	if (disp_row_l < DISP_ROWS) {
		PORTF.OUT = disp_buffer[disp_row_l*DISP_COLUM_BYTES];
		PORTH.OUT = disp_buffer[disp_row_l*DISP_COLUM_BYTES + 1];
		PORTJ.OUT = disp_buffer[disp_row_l*DISP_COLUM_BYTES + 2];
		//no need to OR PORTK, because we know its 0xFF from the row off line
		PORTK.OUT = (disp_buffer[disp_row_l*DISP_COLUM_BYTES + 3]) | 0xF0;
	}
	disp_row_l++;
	//select the column
	if (disp_row_l != 5) {
		PORTK.OUTCLR = disp_linebits[disp_row_l]; //set LED row to on
	} else {
		PORTE.OUTCLR = disp_linebits[disp_row_l]; //set LED row to on
	}
	uint8_t disp_timing_active_delay_cycles_l = disp_timing_active_delay_cycles;
	if (disp_timing_active_delay_cycles_l < (DISP_WITHIN_INT_LIMIT>>2)) {
		//low brightness case
		update_rtc_ticks = disp_timing_idle_line_rtc;
		if (disp_timing_active_delay_cycles_l) {
			_delay_loop_2(disp_timing_active_delay_cycles_l);
		}
		if (disp_row_l != 5) {
			PORTK.OUTSET = disp_linebits[disp_row_l]; //set LED row to off
		} else {
			PORTE.OUTSET = disp_linebits[disp_row_l]; //set LED row to off
		}
		if (disp_row_l >= DISP_ROWS) { // value can be up to 6 if we switch from high to low brightness
			disp_row_l = 0;
		}
	} else {
		if (disp_row_l <= MENU_SCREEN_Y) {
			//happens in High brighness and Maximum brightness case
			update_rtc_ticks = disp_timing_active_rtc;
		} else {
			//only happens in High brighness case
			update_rtc_ticks = disp_timing_idle_rtc;
		}
		//update line position
		if (((disp_row_l == MENU_SCREEN_Y) && (!disp_timing_idle_rtc)) ||
		     (disp_row_l == (MENU_SCREEN_Y+1))) {
			disp_row_l = 0; //faster than a modulo
		}
	}
	/*update rtc compare value
	  While updateing, the CPU may not go to sleep mode, so doing the update
	  at the beginning results in updateing while the code executes and thus
	  results in earlier being able to go to sleep again -> save power
	*/
	uint16_t rtccomp = disp_rtc_comp + update_rtc_ticks;
	if (rtccomp >= disp_rtc_per) {
		rtccomp -= disp_rtc_per;
	}
	while(RTC_STATUS & RTC_SYNCBUSY_bm);
	RTC.COMP = rtccomp;
	disp_rtc_comp = rtccomp;
	disp_row = disp_row_l;
}

ISR(RTC_COMP_vect) {
	if (g_state.performanceUp == 0) {
		g_state.performanceUp = TCC1.CNT;
	}
	disp_update_line();
}

ISR(RTC_OVF_vect) {
	rtc_8thcounter++;
}

void menu_screen_set(SCREENPOS x, SCREENPOS y, unsigned char color) {
	if ((x < MENU_SCREEN_X) && (y < MENU_SCREEN_Y)) {
		x = MENU_SCREEN_X - x -1; //flip horizontal
		y = MENU_SCREEN_Y - y -1; //flip vertical
		unsigned char b = disp_backbuffer[y*DISP_COLUM_BYTES + x/8];
		if (color & 1) {
			b &= ~(1<< (x % 8));
		} else {
			b |= (1<<(x % 8)); //buffer conatins inverted pattern
		}
		disp_backbuffer[y*DISP_COLUM_BYTES + x/8] = b;
	}
}

/*
uint8_t const cBitsSet[16] = {
 0, 1, 1, 2,
 1, 2, 2, 3,
 1, 2, 3, 3,
 2, 3, 3, 4};
*/
uint8_t const cBitsClear[16] = {
 4, 3, 3, 2,
 3, 2, 2, 4,
 3, 2, 1, 1,
 2, 1, 1, 0};

void menu_screen_flush(void) {
	uint8_t i;
	uint8_t dotsOn = 0;
	for (i = 0; i < DISP_TOTAL_BYTES; i++) {
		//cleared bit = lighting dot
		disp_buffer[i] = disp_backbuffer[i];
		dotsOn += cBitsClear[disp_backbuffer[i] >> 4];
		dotsOn += cBitsClear[disp_backbuffer[i] & 0xF];
	}
	g_state.dotsOn = dotsOn;
}

void menu_screen_clear(void) {
	uint8_t i;
	for (i = 0; i < DISP_TOTAL_BYTES; i++) {
		disp_backbuffer[i] = 0xFF;
	}
}

void disp_configure_set(uint8_t brightness, uint16_t refreshrate) {
	if (g_settings.debugRs232 == 3) {
		DbgPrintf_P(PSTR("Disp:%i@%iHz\r\n"), brightness, refreshrate);
	}
	if (brightness) {
		//scale from 0...255 but leave 254 out
		brightness--;
		if (brightness == 254) {
			brightness = 255;
		}
		uint16_t ton_cpu = (uint32_t)(F_CPU/(DISP_ROWS*refreshrate))*(uint32_t)brightness/255;
		uint16_t ton_rtc = (uint32_t)(F_RTC/(DISP_ROWS*refreshrate))*(uint32_t)brightness/255;
		uint16_t toff_rtc =          (F_RTC/(DISP_ROWS*refreshrate) - ton_rtc)*DISP_ROWS;
		uint16_t toff_line_rtc =     (F_RTC/(DISP_ROWS*refreshrate)) - ton_rtc;
		ton_cpu >>= 2; //value used for _delay_loop_2, which needs 4 cycles per iteration
		if (ton_cpu > 255) {
			ton_cpu = 255;
		}
#ifdef ADVANCEDCLOCK
		/*An enabled RFM12 gets trouble if the display is waiting too long in an
		  interrupt. So we increase the brighntess as workaround whenever the RFM12
		  is enabled.
		*/
		//increase bad long interrupt timings from low to high brighntess case
		if (g_state.rfm12modeis) {
			if ((ton_cpu < (DISP_WITHIN_INT_LIMIT>>2)) && //if too short active for high brighntess
				 (ton_cpu > DISP_RFM12_PERMIT_MAX)) {
				/*Just long enough to get to the high brighntess case.
					The fallback will recalculate proper values.
				*/
				ton_cpu = DISP_WITHIN_INT_LIMIT>>2;
			}
		}
#endif
		//fallback: fix values to be safe
		if (ton_rtc < RTC_REQUIRED_SYNC_CYCLES) {
			ton_rtc = RTC_REQUIRED_SYNC_CYCLES;
			toff_rtc = (F_RTC/(DISP_ROWS*refreshrate) - ton_rtc)*DISP_ROWS; //re-calculate
		}
		if (toff_rtc < RTC_REQUIRED_SYNC_CYCLES) {
			toff_rtc = RTC_REQUIRED_SYNC_CYCLES;
		}
		if ((toff_line_rtc < RTC_REQUIRED_SYNC_CYCLES) && (toff_line_rtc)) {
			toff_line_rtc = RTC_REQUIRED_SYNC_CYCLES;
		}

		if (RTC_INTCTRL & RTC_COMPINTLVL_HI_gc) {
			while (disp_row >= 4); //minimize chances for flicker case below
		}
		cli();
		disp_timing_active_rtc = ton_rtc;
		disp_timing_idle_rtc = toff_rtc;
		disp_timing_active_delay_cycles = ton_cpu;
		disp_timing_idle_line_rtc = toff_line_rtc;
		if ((disp_row == MENU_SCREEN_Y) &&
		    ((ton_cpu < (DISP_WITHIN_INT_LIMIT>>2)) || (toff_rtc == 0))) {
			//less flicker hight bright -> low bright transition
			//less flicker hight bright -> max bright transition
			disp_row = MENU_SCREEN_Y-1;
		}
		sei();
		if (g_settings.debugRs232 == 3) {
			DbgPrintf_P(PSTR("tOnR:%u tOffR:%u tOnC:%u tOffLr:%u\r\n"), ton_rtc, toff_rtc, ton_cpu, toff_line_rtc);
		}
		RTC_INTCTRL |= RTC_COMPINTLVL_HI_gc;
	} else {
		//switch LEDs completely off (on is done by the ISR automatically)
		RTC_INTCTRL &= ~RTC_COMPINTLVL_HI_gc;
		PORTE.OUTSET = (1<<6);
		PORTF.OUT = 0xFF;
		PORTH.OUT = 0xFF;
		PORTJ.OUT = 0xFF;
		PORTK.OUT = 0xFF;
		PORTK.OUT = 0xFF;
	}
}

static void totem_port(PORT_t * port) {
	uint8_t i;
	for (i = 0; i < 8; i++) {
		register8_t * pinctrl = (&(port->PIN0CTRL)) + i;
		*pinctrl = PORT_OPC_TOTEM_gc;
	}
}

uint8_t disp_rtc_setup(void) {
	/*column drivers: low = active

	row drivers: low = active. only one row may be active at any time
	Rows 0-5: PortK: 4-7, PortE: 6.
	*/
	//set as output
	PORTE.OUTSET = (1<<6);
	PORTF.OUT = 0xFF;
	PORTH.OUT = 0xFF;
	PORTJ.OUT = 0xFF;
	PORTK.OUT = 0xFF;
	PORTE.DIRSET = (1<<6);
	PORTF.DIR = 0xFF;
	PORTH.DIR = 0xFF;
	PORTJ.DIR = 0xFF;
	PORTK.DIR = 0xFF;
	//disable pullups
	PORTQ.PIN0CTRL = PORT_OPC_TOTEM_gc; //external 32kHz crystal
	PORTQ.PIN1CTRL = PORT_OPC_TOTEM_gc; //external 32kHz crystal
	PORTE.PIN6CTRL = PORT_OPC_TOTEM_gc;
	totem_port(&PORTF);
	totem_port(&PORTH);
	totem_port(&PORTJ);
	totem_port(&PORTK);
	PR_PRGEN &= ~PR_RTC_bm; //activate power of the RTC
	OSC_XOSCCTRL = OSC_X32KLPM_bm | OSC_XOSCSEL1_bm; //low power + 32KHz
	OSC_CTRL |= OSC_XOSCEN_bm; //enable oscillator
	//initialize the screen buffer
	menu_screen_clear(); //set empty drawing screen
	menu_screen_flush(); //copy to framebuffer
	uint8_t timeout = 0;
	while (!(OSC_STATUS & OSC_XOSCRDY_bm) && (timeout < 100)) {
		_delay_loop_2(F_CPU/400); //oscillator start
		timeout++;
	}
	//now the rtc as refresh source
	PMIC.CTRL |= PMIC_HILVLEN_bm |PMIC_MEDLVLEN_bm | PMIC_LOLVLEN_bm;
	if (OSC_STATUS & OSC_XOSCRDY_bm) {
		disp_configure_set(10, 100); //sets the interrupt level for the compare interrupt
		CLK_RTCCTRL = CLK_RTCSRC_TOSC32_gc | CLK_RTCEN_bm;
		while(RTC_STATUS & RTC_SYNCBUSY_bm);
		RTC_PER = disp_rtc_per;
		disp_rtc_comp = 10; //some dummy init value
		RTC_COMP = 10; //some dummy init value
		RTC_CTRL = RTC_PRESCALER_DIV1_gc;
		while(RTC_STATUS & RTC_SYNCBUSY_bm);
		RTC_INTCTRL |= RTC_OVFINTLVL_LO_gc; //overflow. compare int gets set by brightness command
	} else {
		rs232_sendstring_P(PSTR("32kHz oscillator failed\r\n"));
		return 1;
	}
	//select as internal reference clock
/*
	DbgPrintf_P(PSTR("x %u, %u\r\n"), (uint16_t)DFLLRC2M_CALA, (uint16_t)DFLLRC2M_CALB);
	Does not work for unknown reason, likely because of missing secure write enable
	//errata workaround
	OSC_CTRL |= 1<<1; //enable 32khz oscillator
	while (!(OSC_STATUS & OSC_RC32MRDY_bm));
	OSC_DFLLCTRL |= 1;
	DFLLRC32M_CTRL = 2; //enable calibration of internal 2MHz oscillator
	//end errata workaround
	OSC_DFLLCTRL |= 1; //use external 32.768kHz crystal
	DFLLRC2M_CTRL = 1; //enable calibration of internal 2MHz oscillator
	*/
	return 0;
}

#ifdef SYNC_IN_INT
//if the interrupt waits for sync itself, no problem to shut down in main thread
void rtc_waitsafeoff(void) {
}

#else
/*
There are problems:
  If the clock goes to idle but sync is running, updateing RTC.COMP might fail
  -> row flicker.
  Just waiting is not sufficient -> because after waiting there could be a new
  interrupt, resulting in waiting again and loosing sync again.
*/
void rtc_waitsafeoff(void) {
	//wait for sync will take up to 3 RTC clock cycles -> 183 CPU cycles.
	//make sure there is some time until the next int
	uint8_t rtccnt;
	uint8_t rtcmax = RTC.PER;
	if (rtcmax > 2) {
		do {
			while(RTC_STATUS & RTC_SYNCBUSY_bm);
			rtccnt = RTC.CNT;
		} while (((uint8_t)(rtccnt + 2) >= RTC.COMP) || ((rtccnt + 2) >= rtcmax));
	}
}
#endif

#ifdef ADVANCEDCLOCK

//+1, +2 count slower, -1 , -2 count faster, 0 count as expected
void rtc_finecalib(int8_t direction) {
	uint8_t updated = 0;
	if (disp_rtc_per != DISP_RTC_PER + direction) {
		do {
			/* If we update in the wrong moment, this could result in a compare value
			   that is never reached because the new maximum value is smaller than the
			   compare value -> no updates to the display.
			*/
			while (RTC.CNT > DISP_RTC_PER / 2);
			cli();
			while(RTC_STATUS & RTC_SYNCBUSY_bm);
			if (RTC.CNT <= DISP_RTC_PER / 2) {
				disp_rtc_per = DISP_RTC_PER + direction;
				RTC_PER = disp_rtc_per;
				_MemoryBarrier();
				updated = 1;
			}
			sei();
		} while (updated == 0);
	}
}

#endif
