Solartraveler/solarclock/minimatrix/software/matrix-simpleclock/menudata-progmem.c

/*You may need to add #include <avr/pgmspace.h> where you included this file */
const unsigned char menudata[] PROGMEM = {
4, 10, 101, 0, 0, 138, 6, 9, 0, 0, 0, 2, 0, 0, 8, 0, 
0, 14, 10, 1, 1, 0, 7, 4, 10, 2, 2, 0, 0, 0, 10, 3, 
3, 0, 0, 0, 10, 100, 4, 0, 245, 0, 9, 0, 0, 0, 2, 0, 
0, 0, 103, 7, 14, 10, 2, 0, 0, 71, 0, 10, 3, 0, 0, 216, 
0, 10, 4, 4, 0, 245, 0, 9, 0, 0, 0, 2, 0, 0, 0, 109, 
7, 14, 10, 2, 0, 0, 100, 0, 10, 3, 0, 0, 42, 0, 10, 4, 
5, 0, 59, 1, 9, 0, 0, 0, 2, 0, 0, 0, 115, 7, 14, 10, 
2, 0, 0, 129, 0, 10, 3, 0, 0, 71, 0, 10, 4, 6, 0, 94, 
1, 9, 0, 0, 0, 2, 0, 0, 0, 121, 7, 14, 10, 2, 0, 0, 
158, 0, 10, 3, 0, 0, 100, 0, 10, 4, 7, 0, 129, 1, 9, 0, 
0, 0, 2, 0, 0, 0, 126, 7, 14, 10, 2, 0, 0, 187, 0, 10, 
3, 0, 0, 129, 0, 10, 4, 0, 0, 146, 1, 9, 0, 0, 0, 2, 
0, 0, 0, 133, 7, 14, 10, 2, 0, 0, 216, 0, 10, 3, 0, 0, 
158, 0, 10, 4, 0, 0, 88, 3, 9, 0, 0, 0, 2, 0, 0, 0, 
139, 7, 14, 10, 2, 0, 0, 42, 0, 10, 3, 0, 0, 187, 0, 10, 
4, 8, 0, 183, 6, 9, 0, 0, 0, 2, 0, 0, 8, 1, 0, 14, 
10, 1, 1, 0, 42, 0, 10, 2, 9, 0, 24, 1, 10, 3, 5, 0, 
59, 1, 10, 4, 6, 0, 94, 1, 9, 0, 0, 0, 2, 0, 0, 8, 
2, 0, 14, 10, 1, 1, 0, 42, 0, 10, 2, 4, 0, 245, 0, 10, 
3, 5, 0, 59, 1, 10, 4, 6, 0, 94, 1, 9, 0, 0, 0, 2, 
0, 0, 8, 3, 0, 14, 10, 1, 1, 0, 71, 0, 10, 2, 10, 0, 
0, 0, 10, 3, 11, 0, 0, 0, 10, 4, 12, 0, 0, 0, 9, 0, 
0, 0, 2, 0, 0, 8, 4, 0, 14, 10, 1, 1, 0, 100, 0, 10, 
2, 13, 0, 0, 0, 10, 3, 14, 0, 0, 0, 10, 4, 15, 0, 0, 
0, 9, 0, 0, 0, 2, 0, 0, 8, 5, 0, 14, 10, 1, 1, 0, 
129, 0, 9, 0, 0, 0, 2, 0, 0, 0, 147, 7, 14, 10, 1, 0, 
0, 158, 0, 10, 2, 0, 0, 181, 1, 10, 3, 0, 0, 100, 2, 10, 
4, 16, 0, 135, 2, 9, 0, 0, 0, 2, 0, 0, 0, 155, 7, 14, 
10, 1, 0, 0, 158, 0, 10, 2, 0, 0, 216, 1, 10, 3, 0, 0, 
146, 1, 10, 4, 0, 0, 170, 2, 9, 0, 0, 0, 2, 0, 0, 0, 
162, 7, 14, 10, 1, 0, 0, 158, 0, 10, 2, 0, 0, 251, 1, 10, 
3, 0, 0, 181, 1, 10, 4, 0, 0, 199, 2, 9, 0, 0, 0, 2, 
0, 0, 0, 169, 7, 14, 10, 1, 0, 0, 158, 0, 10, 2, 0, 0, 
30, 2, 10, 3, 0, 0, 216, 1, 10, 4, 0, 0, 228, 2, 9, 0, 
0, 0, 2, 0, 0, 0, 177, 7, 14, 10, 1, 0, 0, 158, 0, 10, 
2, 0, 0, 65, 2, 10, 3, 0, 0, 251, 1, 10, 4, 0, 0, 1, 
3, 9, 0, 0, 0, 2, 0, 0, 0, 185, 7, 14, 10, 1, 0, 0, 
158, 0, 10, 2, 0, 0, 100, 2, 10, 3, 0, 0, 30, 2, 10, 4, 
0, 0, 30, 3, 9, 0, 0, 0, 2, 0, 0, 0, 192, 7, 14, 10, 
1, 0, 0, 158, 0, 10, 2, 0, 0, 146, 1, 10, 3, 0, 0, 65, 
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
